shanebdavis/hexfinity/diagrams/interlock-profile.png

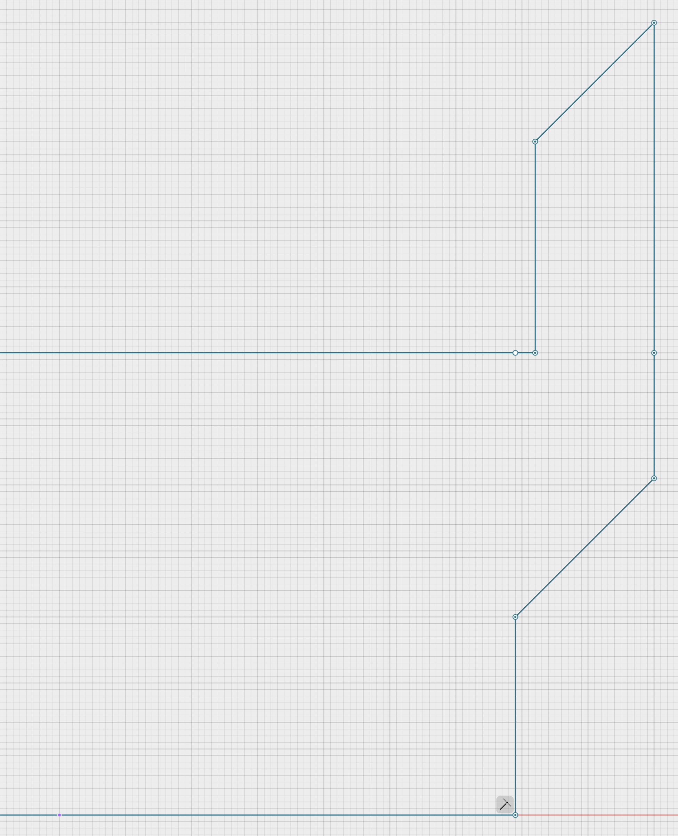
diagrams/interlock-profile.png
