shanebdavis/hexfinity/models/hexfinity-to-gridfinity/Hexfinity-Gridfinity Adapter Arrow Extension 2x.stl

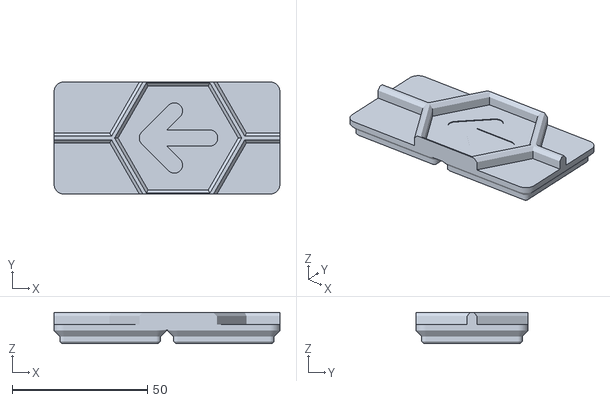
[picture p35: CAD file, 2025-04-02]
models/hexfinity-to-gridfinity/Hexfinity-Gridfinity Adapter Arrow Extension 2x.stl
83.5 x 41.5 x 11.5
