shanebdavis/hexfinity/models/roll-hexfinity cut-outs/Roll Hexfinity Brick 3-path cut-out.stl

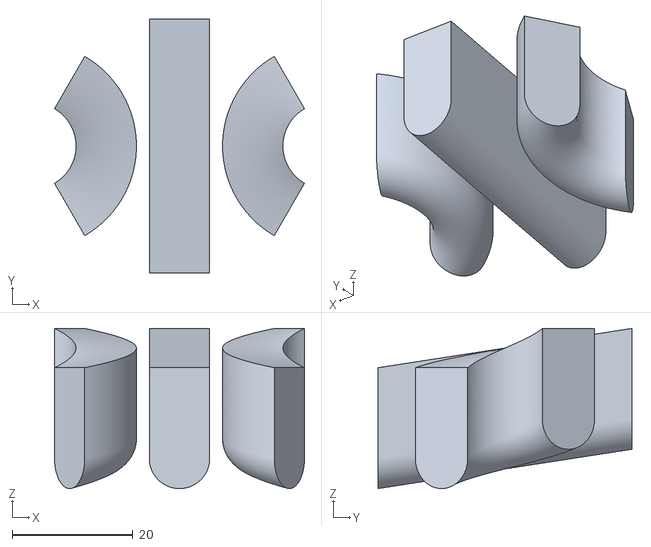
[picture p36: CAD file, 2025-02-22]
models/roll-hexfinity cut-outs/Roll Hexfinity Brick 3-path cut-out.stl
41.4 x 42.0 x 26.5
