shanebdavis/hexfinity/models/hexfinity-bases/Hexfinity 0mm Base 4-hex Line.stl

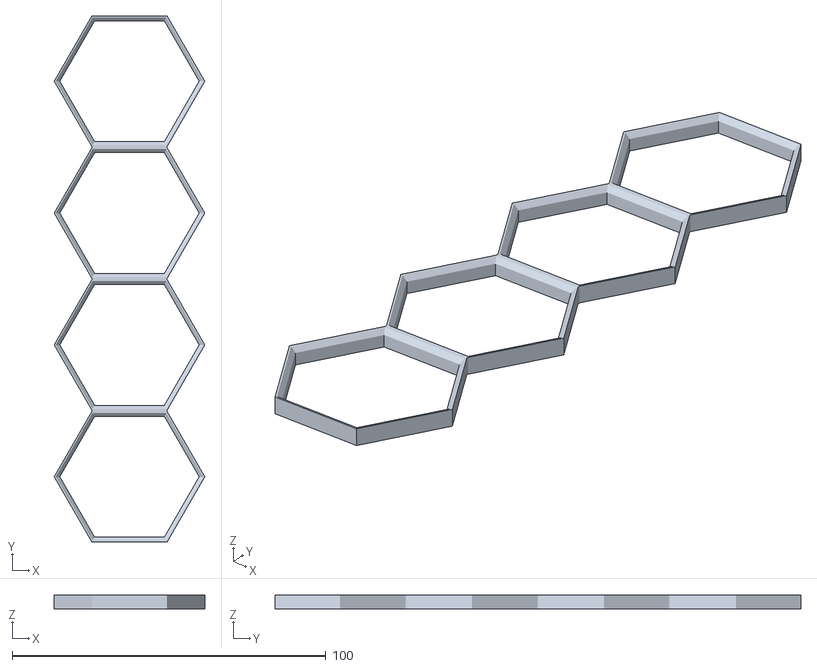
[picture p37: CAD file, 2025-03-15]
models/hexfinity-bases/Hexfinity 0mm Base 4-hex Line.stl
48.0 x 167.6 x 4.50
