shanebdavis/hexfinity/models/hexfinity-plates/Hexfinity 7mm Plate 7-hex 2-3-2.stl

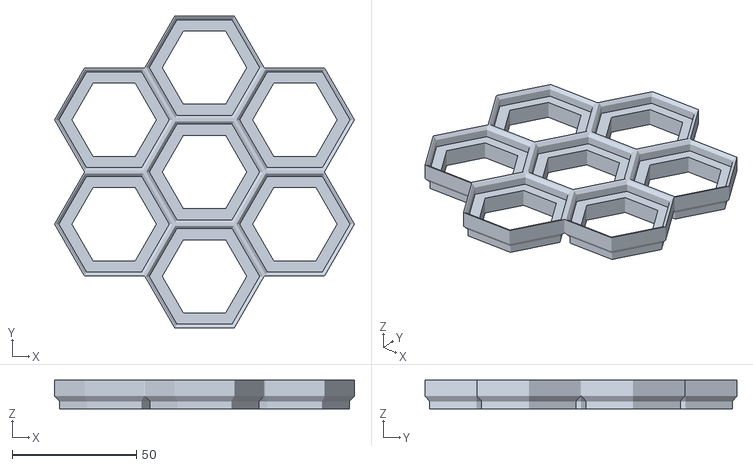
[picture p38: CAD file, 2025-03-15]
models/hexfinity-plates/Hexfinity 7mm Plate 7-hex 2-3-2.stl
120.7 x 125.6 x 11.5
