shanebdavis/hexfinity/models/hexfinity-to-gridfinity/Hexfinity-QuadGridfinity Adapter Extension 4x.stl

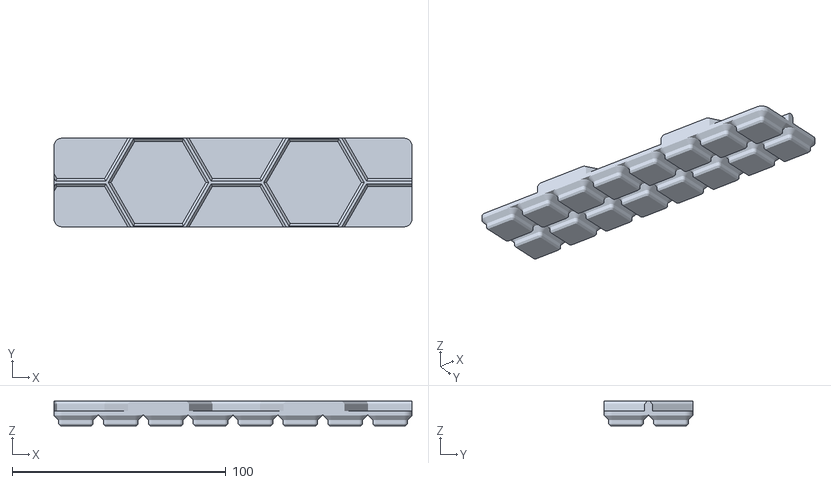
[picture p39: CAD file, 2025-04-02]
models/hexfinity-to-gridfinity/Hexfinity-QuadGridfinity Adapter Extension 4x.stl
167.5 x 41.5 x 11.5
