shanebdavis/hexfinity/models/roll-hexfinity/Roll Hexfinity 14mm Flat 3-path.stl

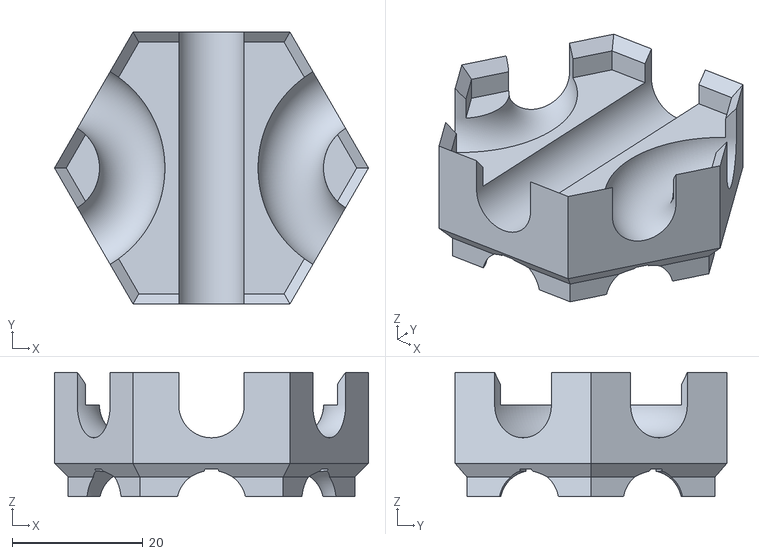
[picture p41: CAD file, 2025-02-22]
models/roll-hexfinity/Roll Hexfinity 14mm Flat 3-path.stl
48.0 x 41.6 x 19.0
