shanebdavis/hexfinity/models/hexfinity-bases/Hexfinity 0mm Base 30-hex 5x6.stl

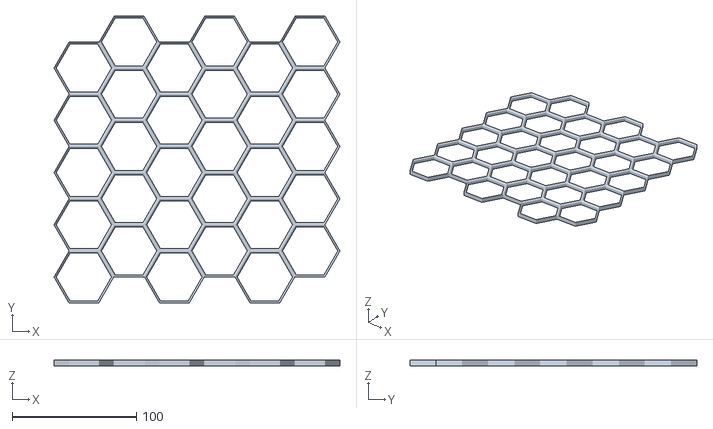
[picture p42: CAD file, 2025-03-15]
models/hexfinity-bases/Hexfinity 0mm Base 30-hex 5x6.stl
229.9 x 230.6 x 4.50
