shanebdavis/hexfinity/models/hexfinity-plates/Hexfinity 7mm Plate 1-hex.stl

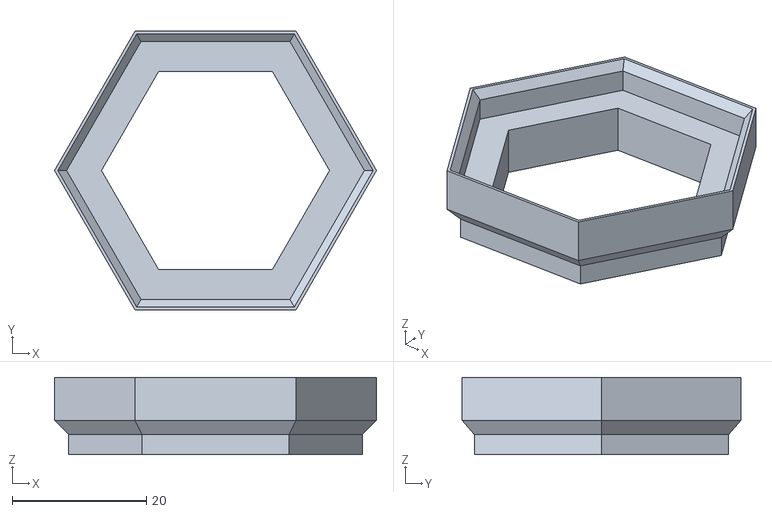
[picture p43: CAD file, 2025-03-15]
models/hexfinity-plates/Hexfinity 7mm Plate 1-hex.stl
48.0 x 41.6 x 11.5
