shanebdavis/hexfinity/models/roll-hexfinity cut-outs/Roll Hexfinity Brick 5-merge cut-out.stl

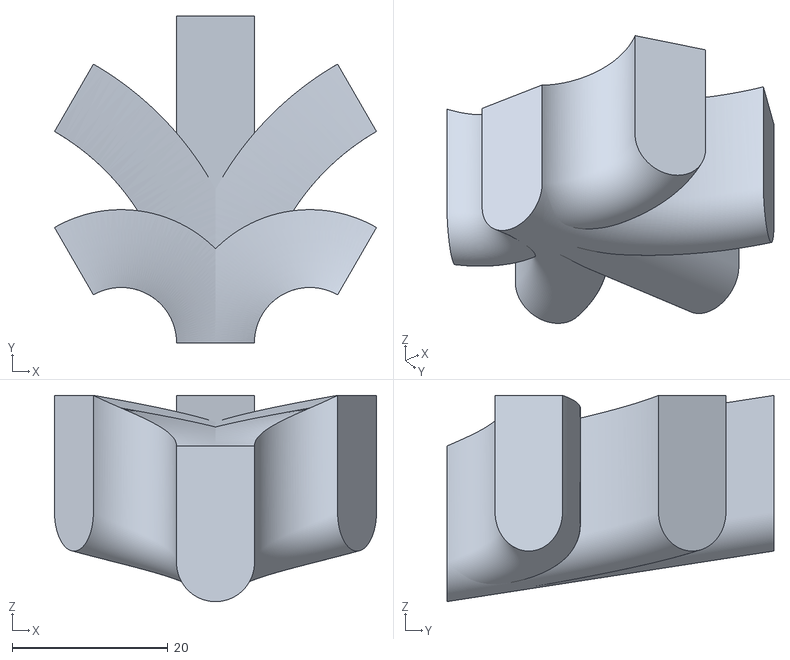
[picture p45: CAD file, 2025-02-22]
models/roll-hexfinity cut-outs/Roll Hexfinity Brick 5-merge cut-out.stl
41.4 x 42.0 x 26.5
