shanebdavis/hexfinity/models/roll-hexfinity/Roll Hexfinity 14mm Sink.stl

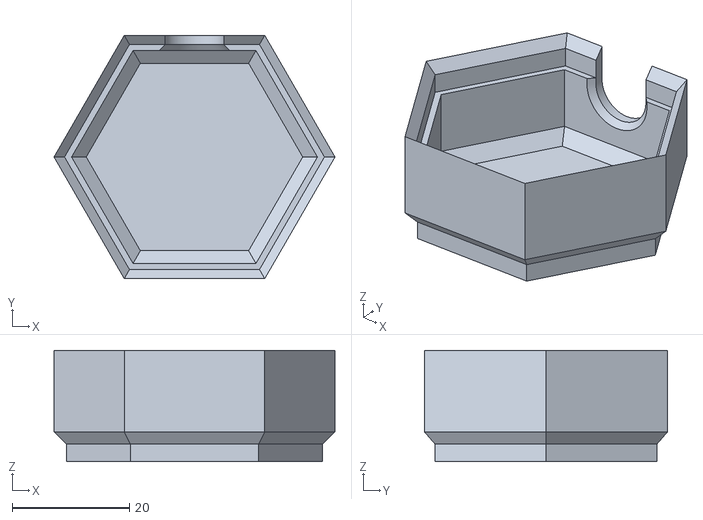
[picture p46: CAD file, 2025-02-22]
models/roll-hexfinity/Roll Hexfinity 14mm Sink.stl
48.0 x 41.6 x 19.0
