shanebdavis/hexfinity/models/hexfinity-bases/Hexfinity 0mm Base 3-hex U.stl

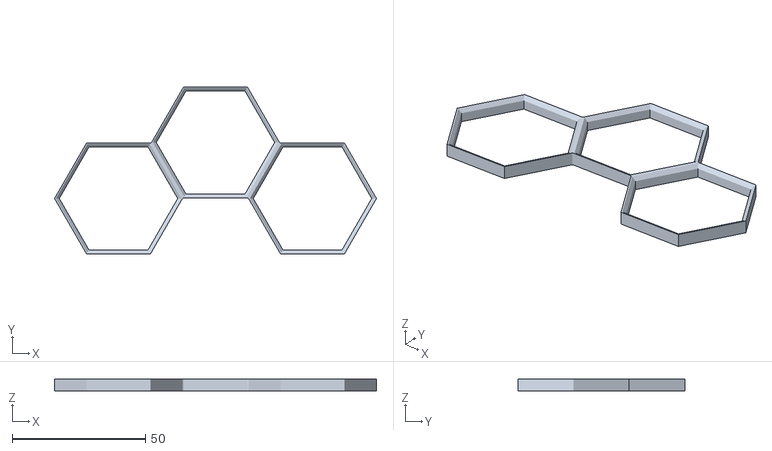
[picture p47: CAD file, 2025-03-15]
models/hexfinity-bases/Hexfinity 0mm Base 3-hex U.stl
120.7 x 62.6 x 4.50
