shanebdavis/hexfinity/models/hexfinity-plates/Hexfinity 7mm Plate 3-hex radial.stl

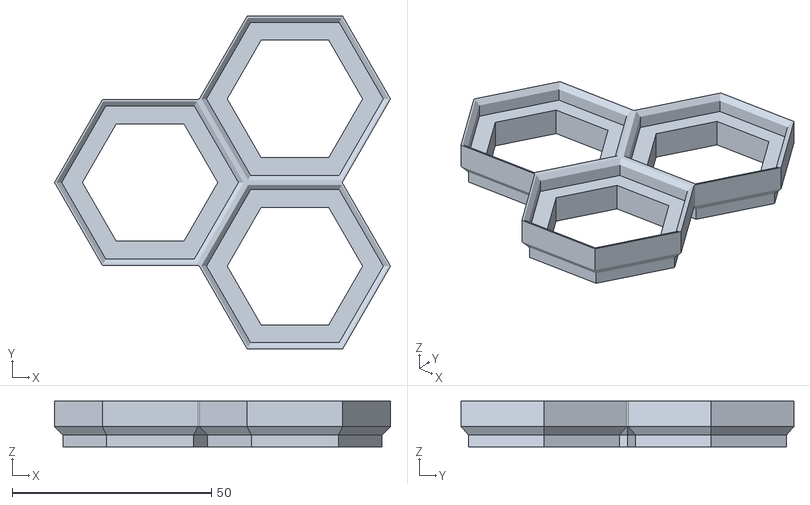
[picture p48: CAD file, 2025-03-15]
models/hexfinity-plates/Hexfinity 7mm Plate 3-hex radial.stl
84.4 x 83.6 x 11.5
