shanebdavis/hexfinity/models/roll-hexfinity cut-outs/Roll Hexfinity bottom cut out.stl

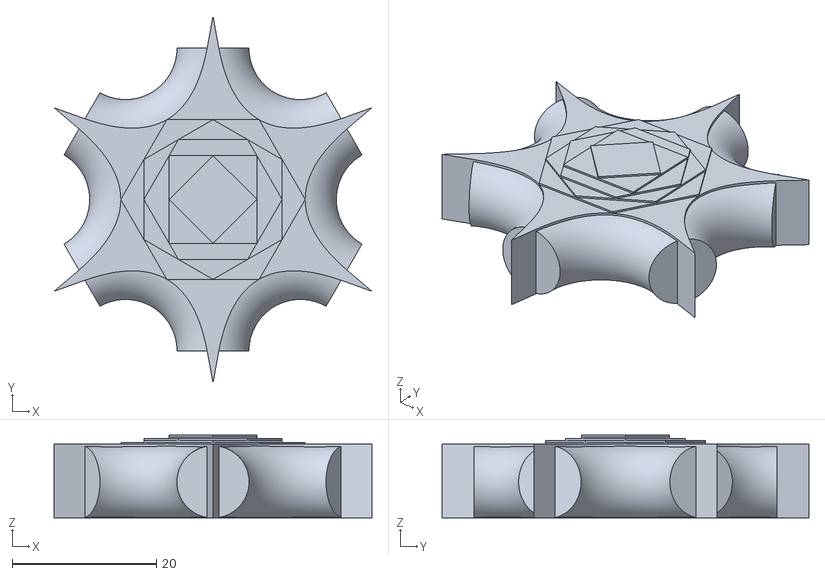
[picture p50: CAD file, 2025-02-22]
models/roll-hexfinity cut-outs/Roll Hexfinity bottom cut out.stl
44.1 x 50.9 x 11.5
