shanebdavis/hexfinity/models/roll-hexfinity/Roll Hexfinity 21mm Brick 3-path.stl

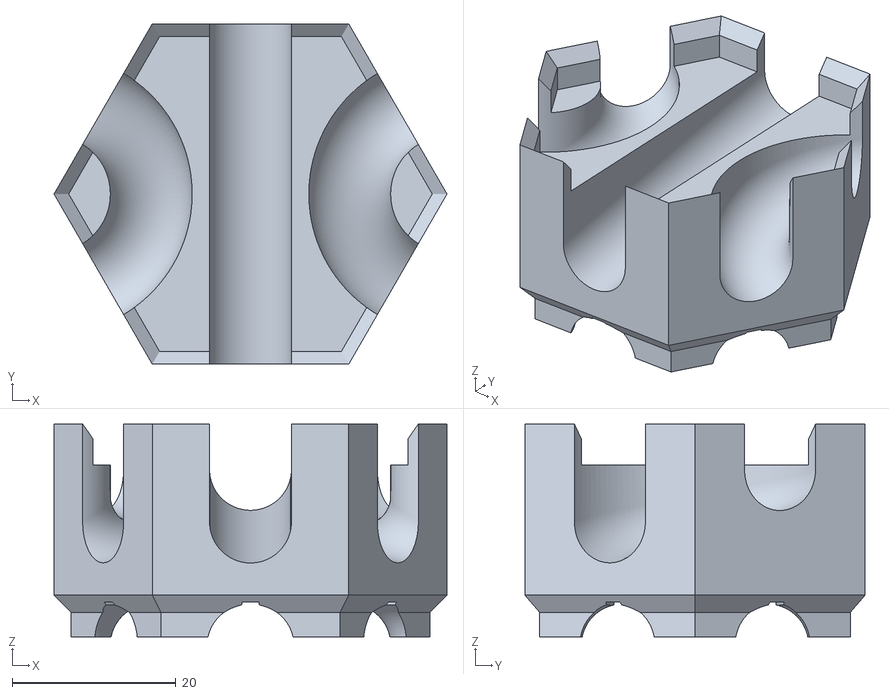
[picture p51: CAD file, 2025-02-22]
models/roll-hexfinity/Roll Hexfinity 21mm Brick 3-path.stl
48.0 x 41.6 x 26.0
