shanebdavis/hexfinity/models/hexfinity-bases/Hexfinity 0mm Base 5-hex line.stl

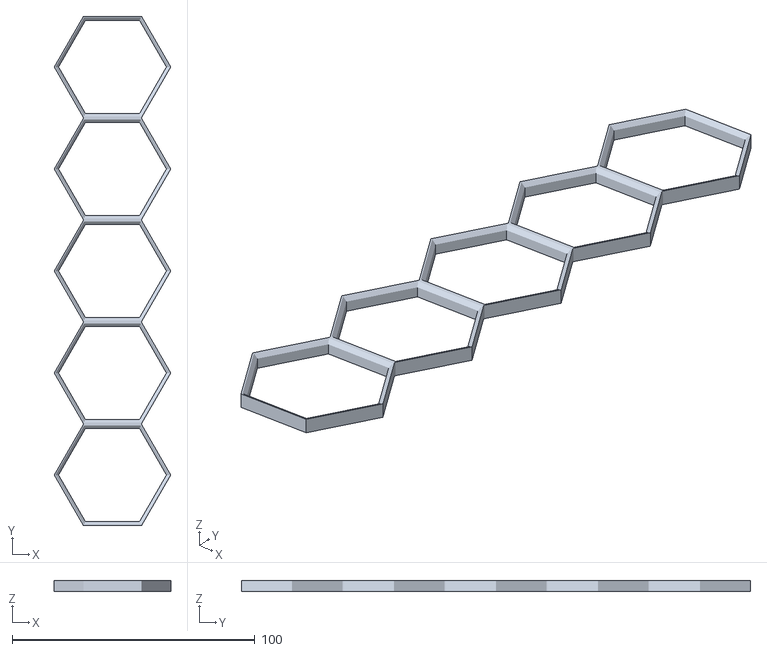
[picture p52: CAD file, 2025-03-15]
models/hexfinity-bases/Hexfinity 0mm Base 5-hex line.stl
48.0 x 209.6 x 4.50
