shanebdavis/hexfinity/models/hexfinity-plates/Hexfinity 7mm Plate 3-hex U.stl

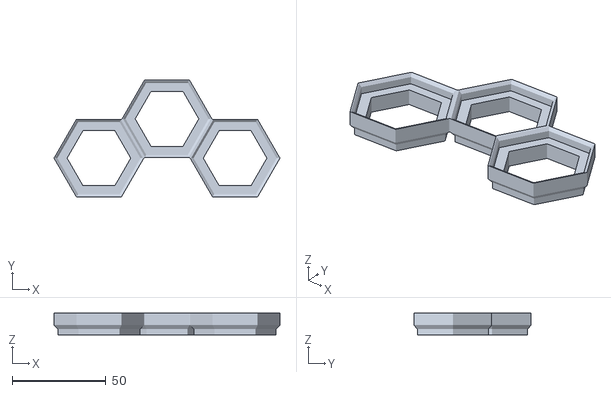
[picture p53: CAD file, 2025-03-15]
models/hexfinity-plates/Hexfinity 7mm Plate 3-hex U.stl
120.7 x 62.6 x 11.5
