shanebdavis/hexfinity/models/roll-hexfinity cut-outs/Roll Hexfinity Brick 2-split cut-out.stl

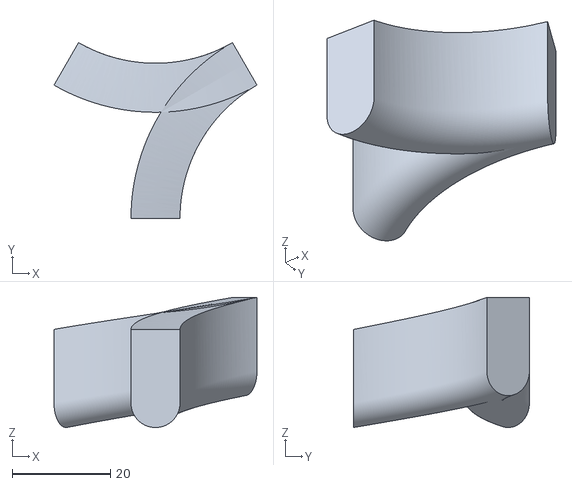
[picture p54: CAD file, 2025-02-22]
models/roll-hexfinity cut-outs/Roll Hexfinity Brick 2-split cut-out.stl
41.4 x 35.8 x 26.5
