shanebdavis/hexfinity/models/hexfinity-bases/Hexfinity 0mm Base 10-hex 5x2.stl

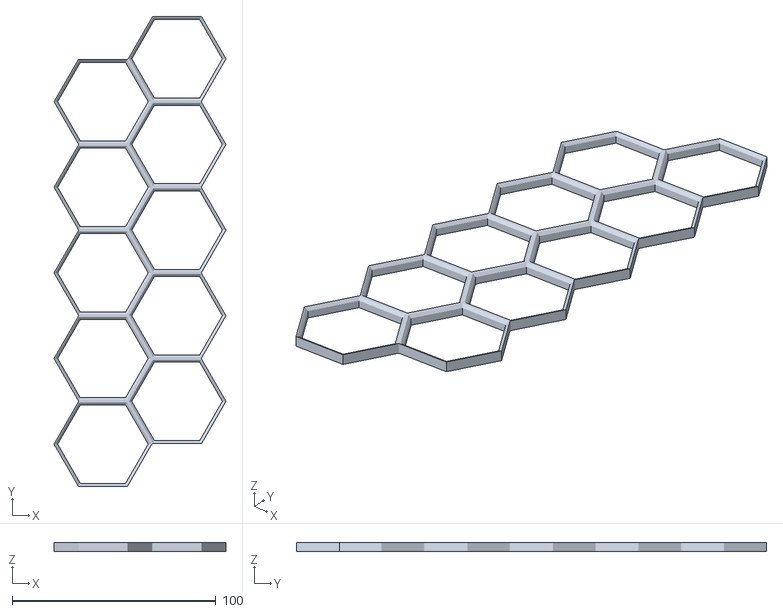
[picture p55: CAD file, 2025-03-15]
models/hexfinity-bases/Hexfinity 0mm Base 10-hex 5x2.stl
84.4 x 230.6 x 4.50
