shanebdavis/hexfinity/models/hexfinity-bases/Hexfinity 0mm Base 3-hex Line.stl

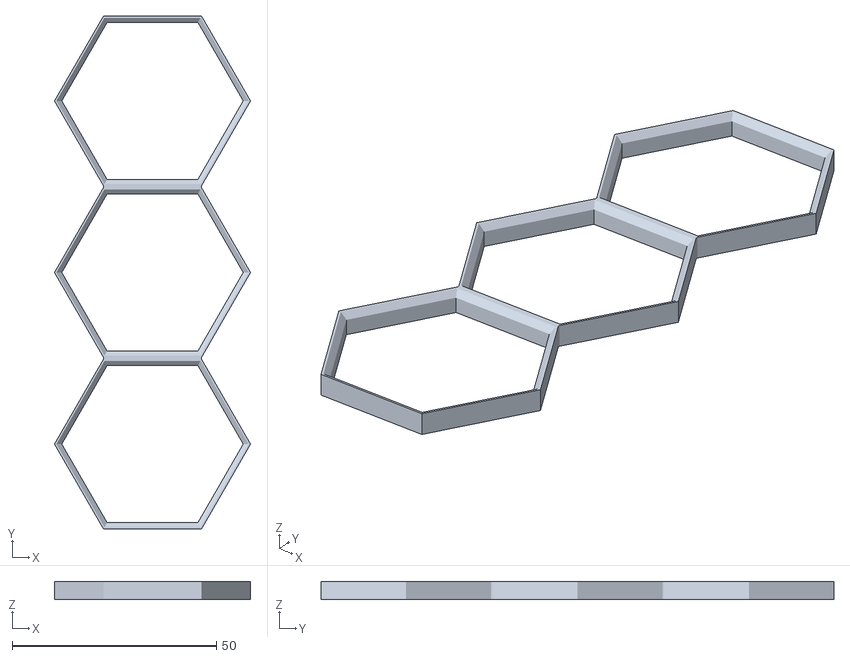
[picture p57: CAD file, 2025-03-15]
models/hexfinity-bases/Hexfinity 0mm Base 3-hex Line.stl
48.0 x 125.6 x 4.50
