shanebdavis/hexfinity/models/roll-hexfinity/Roll Hexfinity 7mm Plate 1-hex.stl

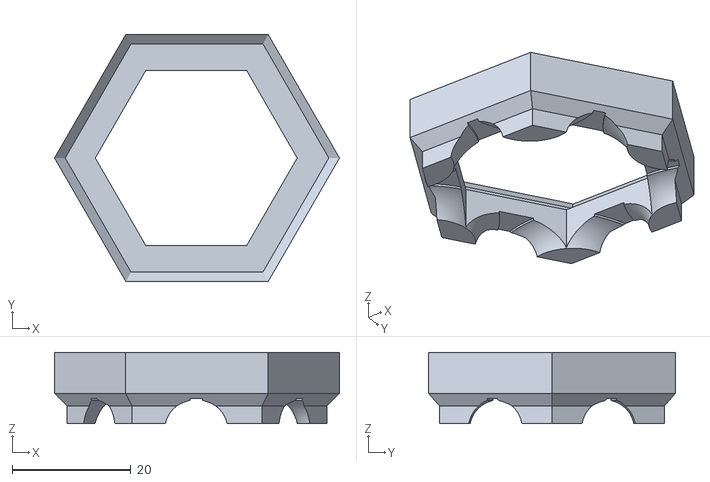
[picture p58: CAD file, 2025-02-22]
models/roll-hexfinity/Roll Hexfinity 7mm Plate 1-hex.stl
48.0 x 41.6 x 12.0
