shanebdavis/hexfinity/models/hexfinity-bases/Hexfinity 0mm Base 3-hex radial.stl

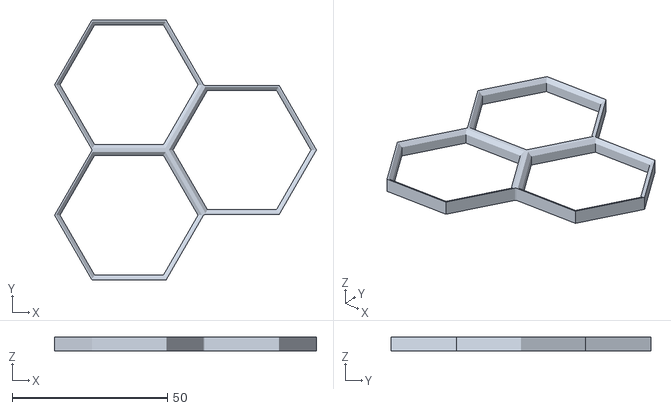
[picture p59: CAD file, 2025-03-15]
models/hexfinity-bases/Hexfinity 0mm Base 3-hex radial.stl
84.4 x 83.6 x 4.50
