shanebdavis/hexfinity/models/hexfinity-to-gridfinity/Hexfinity-Gridfinity Adapter Extension 3x.stl

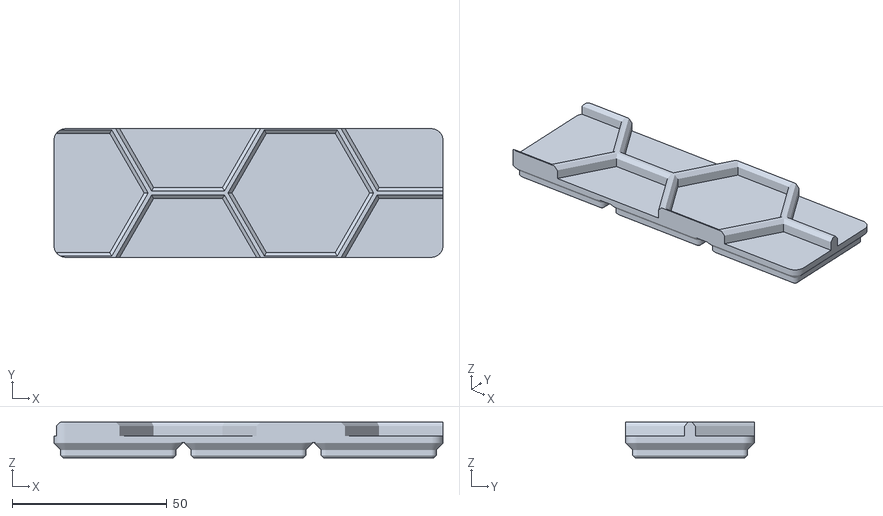
[picture p60: CAD file, 2025-04-02]
models/hexfinity-to-gridfinity/Hexfinity-Gridfinity Adapter Extension 3x.stl
125.5 x 41.5 x 11.5
