shanebdavis/hexfinity/models/hexfinity-bases/Hexfinity 0mm Base 1-hex.stl

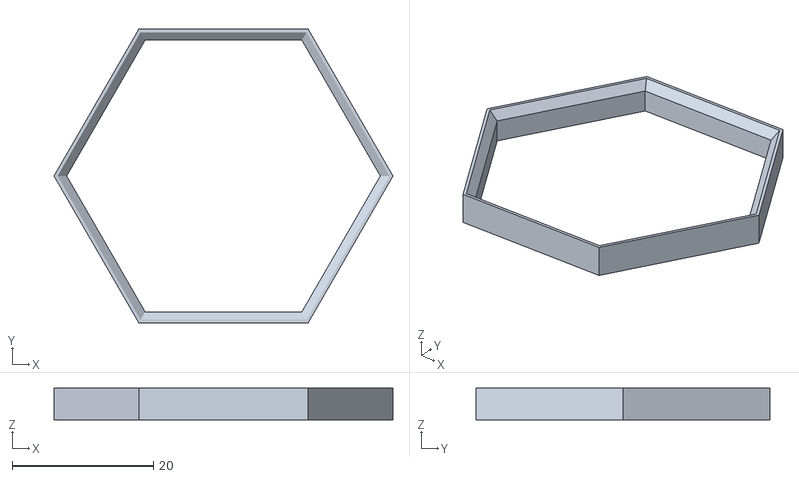
[picture p61: CAD file, 2025-03-15]
models/hexfinity-bases/Hexfinity 0mm Base 1-hex.stl
48.0 x 41.6 x 4.50
