shanebdavis/hexfinity/models/hexfinity-bases/Hexfinity 0mm Base 14-hex 4-3-4-3.stl

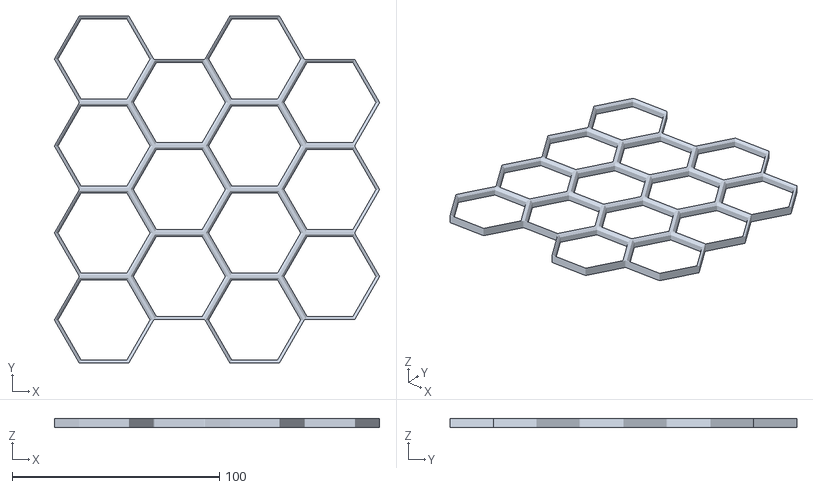
[picture p62: CAD file, 2025-03-15]
models/hexfinity-bases/Hexfinity 0mm Base 14-hex 4-3-4-3.stl
157.1 x 167.6 x 4.50
