shanebdavis/hexfinity/models/hexfinity-to-gridfinity/Hexfinity-QuadGridfinity Adapter Extension 1x.stl

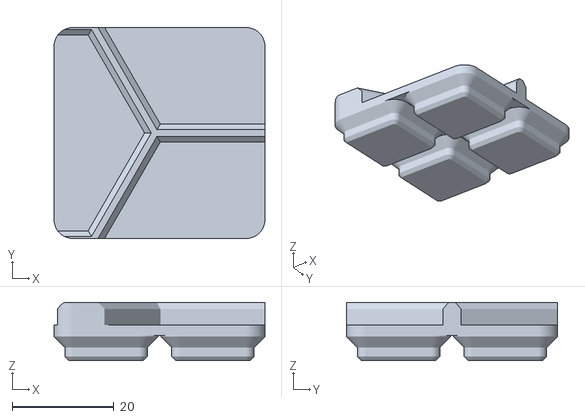
[picture p63: CAD file, 2025-04-02]
models/hexfinity-to-gridfinity/Hexfinity-QuadGridfinity Adapter Extension 1x.stl
41.5 x 41.5 x 11.5
