shanebdavis/hexfinity/models/hexfinity-bases/Hexfinity 0mm Base 4-hex.stl

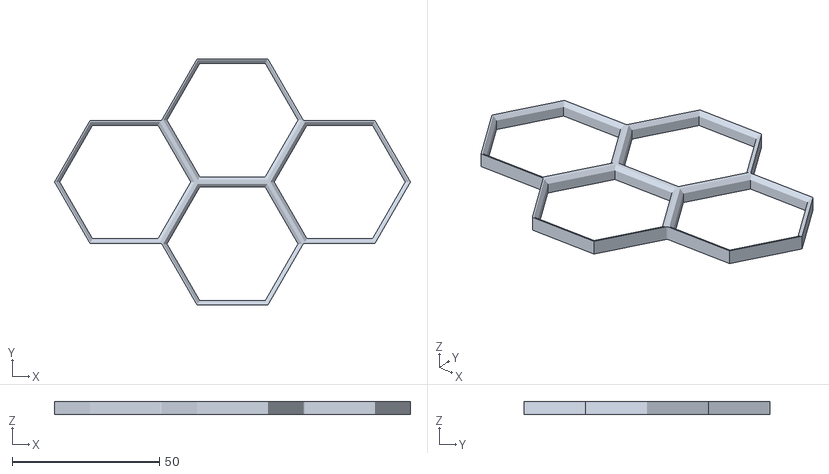
[picture p64: CAD file, 2025-03-15]
models/hexfinity-bases/Hexfinity 0mm Base 4-hex.stl
120.7 x 83.6 x 4.50
