shanebdavis/hexfinity/models/hexfinity-to-gridfinity/Hexfinity-QuadGridfinity Adapter Arrow Extension 2x.stl

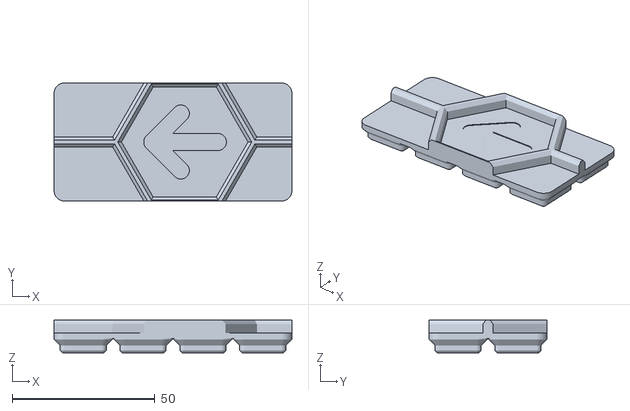
[picture p66: CAD file, 2025-04-02]
models/hexfinity-to-gridfinity/Hexfinity-QuadGridfinity Adapter Arrow Extension 2x.stl
83.5 x 41.5 x 11.5
